yanataka60/MZ-700_SD-NiseRamFile/source/boot.h

uint8_t __attribute__  ((aligned(sizeof(unsigned char *)*4096))) mz1r12[0x10000] = {
0xA5,0x0A,0x00,0x32,0x00,0x32,0xCA,0x21,0x12,0x11,0x00,0x22,0x21,0x00,0x00,0x01,
0x00,0x10,0xED,0xB0,0xD3,0xE0,0x11,0x00,0x00,0x21,0x00,0x22,0x01,0x00,0x10,0xED,
0xB0,0x11,0x00,0xC1,0x21,0x67,0x32,0x01,0xB1,0x09,0xED,0xB0,0x21,0x85,0x00,0x22,
0x01,0x00,0x21,0x00,0xC1,0x22,0xF7,0x00,0x21,0x00,0x00,0x22,0xAB,0x00,0x3E,0xC3,
0x32,0x36,0x04,0x21,0x04,0xC1,0x22,0x37,0x04,0x32,0x75,0x04,0x21,0x07,0xC1,0x22,
0x76,0x04,0x32,0xD8,0x04,0x21,0x0A,0xC1,0x22,0xD9,0x04,0x32,0xF8,0x04,0x21,0x0D,
0xC1,0x22,0xF9,0x04,0x32,0x88,0x05,0x21,0x10,0xC1,0x22,0x89,0x05,0xC3,0x00,0x00,
0x00,0xC3,0x13,0xC1,0xC3,0xFF,0xC7,0xC3,0x4C,0xC8,0xC3,0x7F,0xC8,0xC3,0x63,0xC9,
0xC3,0x95,0xC9,0xCD,0x78,0xC1,0x11,0xA3,0x11,0x1A,0xFE,0x2A,0xC2,0x8C,0xC2,0x13,
0x1A,0xFE,0x46,0xC2,0x8C,0xC2,0x13,0x1A,0xFE,0x44,0xC2,0x8C,0xC2,0x13,0x1A,0xFE,
0x20,0x28,0x50,0xFE,0x2F,0x28,0x4C,0xFE,0x0D,0x20,0x0D,0xD5,0x21,0xF5,0xC7,0x13,
0x01,0x05,0x00,0xED,0xB0,0xD1,0x18,0x3B,0xFE,0x53,0xCA,0xEF,0xC1,0xFE,0x41,0xCA,
0x02,0xC3,0xFE,0x4C,0xCA,0x0D,0xC3,0xFE,0x44,0xCA,0xA8,0xC3,0xFE,0x52,0xCA,0xE5,
0xC3,0xFE,0x50,0xCA,0x12,0xC4,0xFE,0x43,0xCA,0xB7,0xC4,0xFE,0x4D,0xCA,0xE4,0xC4,
0xFE,0x57,0xCA,0x69,0xC5,0xC3,0xC8,0xC9,0x3E,0x8A,0xD3,0xA3,0x3E,0x00,0xD3,0xA0,
0xD3,0xA2,0xC9,0x3E,0x81,0xCD,0x22,0xC6,0xCD,0x9C,0xC1,0x31,0x00,0xD8,0x21,0x76,
0xCA,0x11,0x00,0xD4,0x01,0x3B,0x00,0xED,0xB0,0xC3,0x00,0xD4,0x21,0xF1,0x10,0x06,
0x11,0xCD,0xB6,0xC5,0x77,0x23,0x05,0x20,0xF8,0x11,0x36,0xC6,0xCD,0x15,0x00,0x11,
0xF1,0x10,0xCD,0x15,0x00,0xCD,0x06,0x00,0x21,0x04,0x11,0xCD,0xB6,0xC5,0x77,0x23,
0xCD,0xB6,0xC5,0x77,0x21,0x02,0x11,0xCD,0xB6,0xC5,0x77,0x23,0xCD,0xB6,0xC5,0x77,
0x21,0x06,0x11,0xCD,0xB6,0xC5,0x77,0x23,0xCD,0xB6,0xC5,0x77,0xC9,0xED,0x5B,0x02,
0x11,0x2A,0x04,0x11,0xCD,0xB6,0xC5,0x77,0x1B,0x7A,0xB3,0x23,0x20,0xF6,0xC9,0x13,
0x13,0xD5,0xCD,0x10,0x04,0x38,0x3B,0x22,0x04,0x11,0xD1,0x13,0x13,0x13,0x13,0x13,
0xD5,0xCD,0x10,0x04,0x38,0x2C,0xE5,0xED,0x4B,0x04,0x11,0xED,0x42,0xE1,0x28,0x22,
0x38,0x20,0x22,0x02,0x11,0xD1,0x13,0x13,0x13,0x13,0x13,0xD5,0xCD,0x10,0x04,0x38,
0x11,0x22,0x06,0x11,0xD1,0x13,0x13,0x13,0x13,0x13,0x1A,0xFE,0x31,0x38,0x08,0xEB,
0x18,0x0F,0x11,0x80,0xC6,0x18,0x4F,0x11,0x90,0xC6,0x18,0x4A,0x11,0xA2,0xC6,0x18,
0x45,0x3E,0x80,0xCD,0x08,0xC6,0xA7,0xC2,0x5C,0xC2,0xCD,0xA6,0xC2,0xCD,0xB6,0xC5,
0xA7,0x20,0x09,0xCD,0xEB,0xC2,0x11,0x49,0xC6,0x18,0x2B,0xD1,0xFE,0xF0,0x20,0x05,
0x11,0xB2,0xC6,0x18,0x21,0xFE,0xF1,0x20,0x05,0x11,0xCB,0xC6,0x18,0x18,0xFE,0xF3,
0x20,0x05,0x11,0xD9,0xC6,0x18,0x0F,0xFE,0xF4,0x20,0x05,0x11,0xA2,0xC6,0x18,0x06,
0xCD,0xC3,0x03,0x11,0xEE,0xC7,0xCD,0x15,0x00,0xCD,0x06,0x00,0x21,0x4E,0x01,0x7E,
0xFE,0x50,0xCA,0x82,0x00,0xFE,0x4E,0xCA,0x82,0x00,0x21,0xEB,0x06,0x7E,0xFE,0x4D,
0xCA,0xAD,0x00,0xC3,0x00,0x00,0xE5,0x06,0x20,0x7E,0xCD,0xC9,0xC5,0x23,0x05,0x20,
0xF8,0x3E,0x0D,0xCD,0xC9,0xC5,0xE1,0x06,0x10,0x7E,0xCD,0xC9,0xC5,0x23,0x05,0x20,
0xF8,0x3E,0x0D,0xCD,0xC9,0xC5,0x21,0x04,0x11,0x7E,0xCD,0xC9,0xC5,0x23,0x7E,0xCD,
0xC9,0xC5,0x21,0x02,0x11,0x7E,0xCD,0xC9,0xC5,0x23,0x7E,0xCD,0xC9,0xC5,0x21,0x06,
0x11,0x7E,0xCD,0xC9,0xC5,0x23,0x7E,0xCD,0xC9,0xC5,0xC9,0x2A,0x02,0x11,0xEB,0x2A,
0x04,0x11,0x7E,0xCD,0xC9,0xC5,0x7C,0xBA,0x20,0x04,0x7D,0xBB,0x28,0x03,0x23,0x18,
0xF1,0xC9,0x3E,0x82,0xCD,0x22,0xC6,0x11,0x58,0xC6,0xC3,0x86,0xC2,0x13,0x21,0xFA,
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
};
